angelgabrieljacintohuayllasco/G-Mini-Agent-Home/hardware/templates/pyramid-laptop-15.6-pieces.dxf

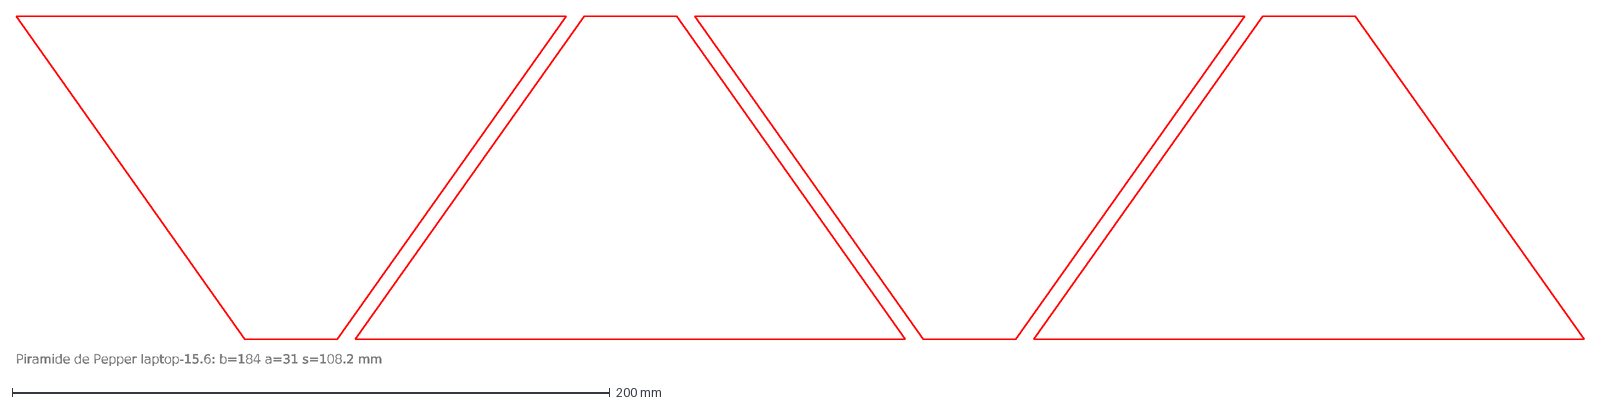
[picture p23: CAD file, 2026-10-08]
hardware/templates/pyramid-laptop-15.6-pieces.dxf
Piramide de Pepper laptop-15.6: b=184 a=31 s=108.2 mm
