angelgabrieljacintohuayllasco/G-Mini-Agent-Home/hardware/templates/pyramid-tv-32-net.dxf

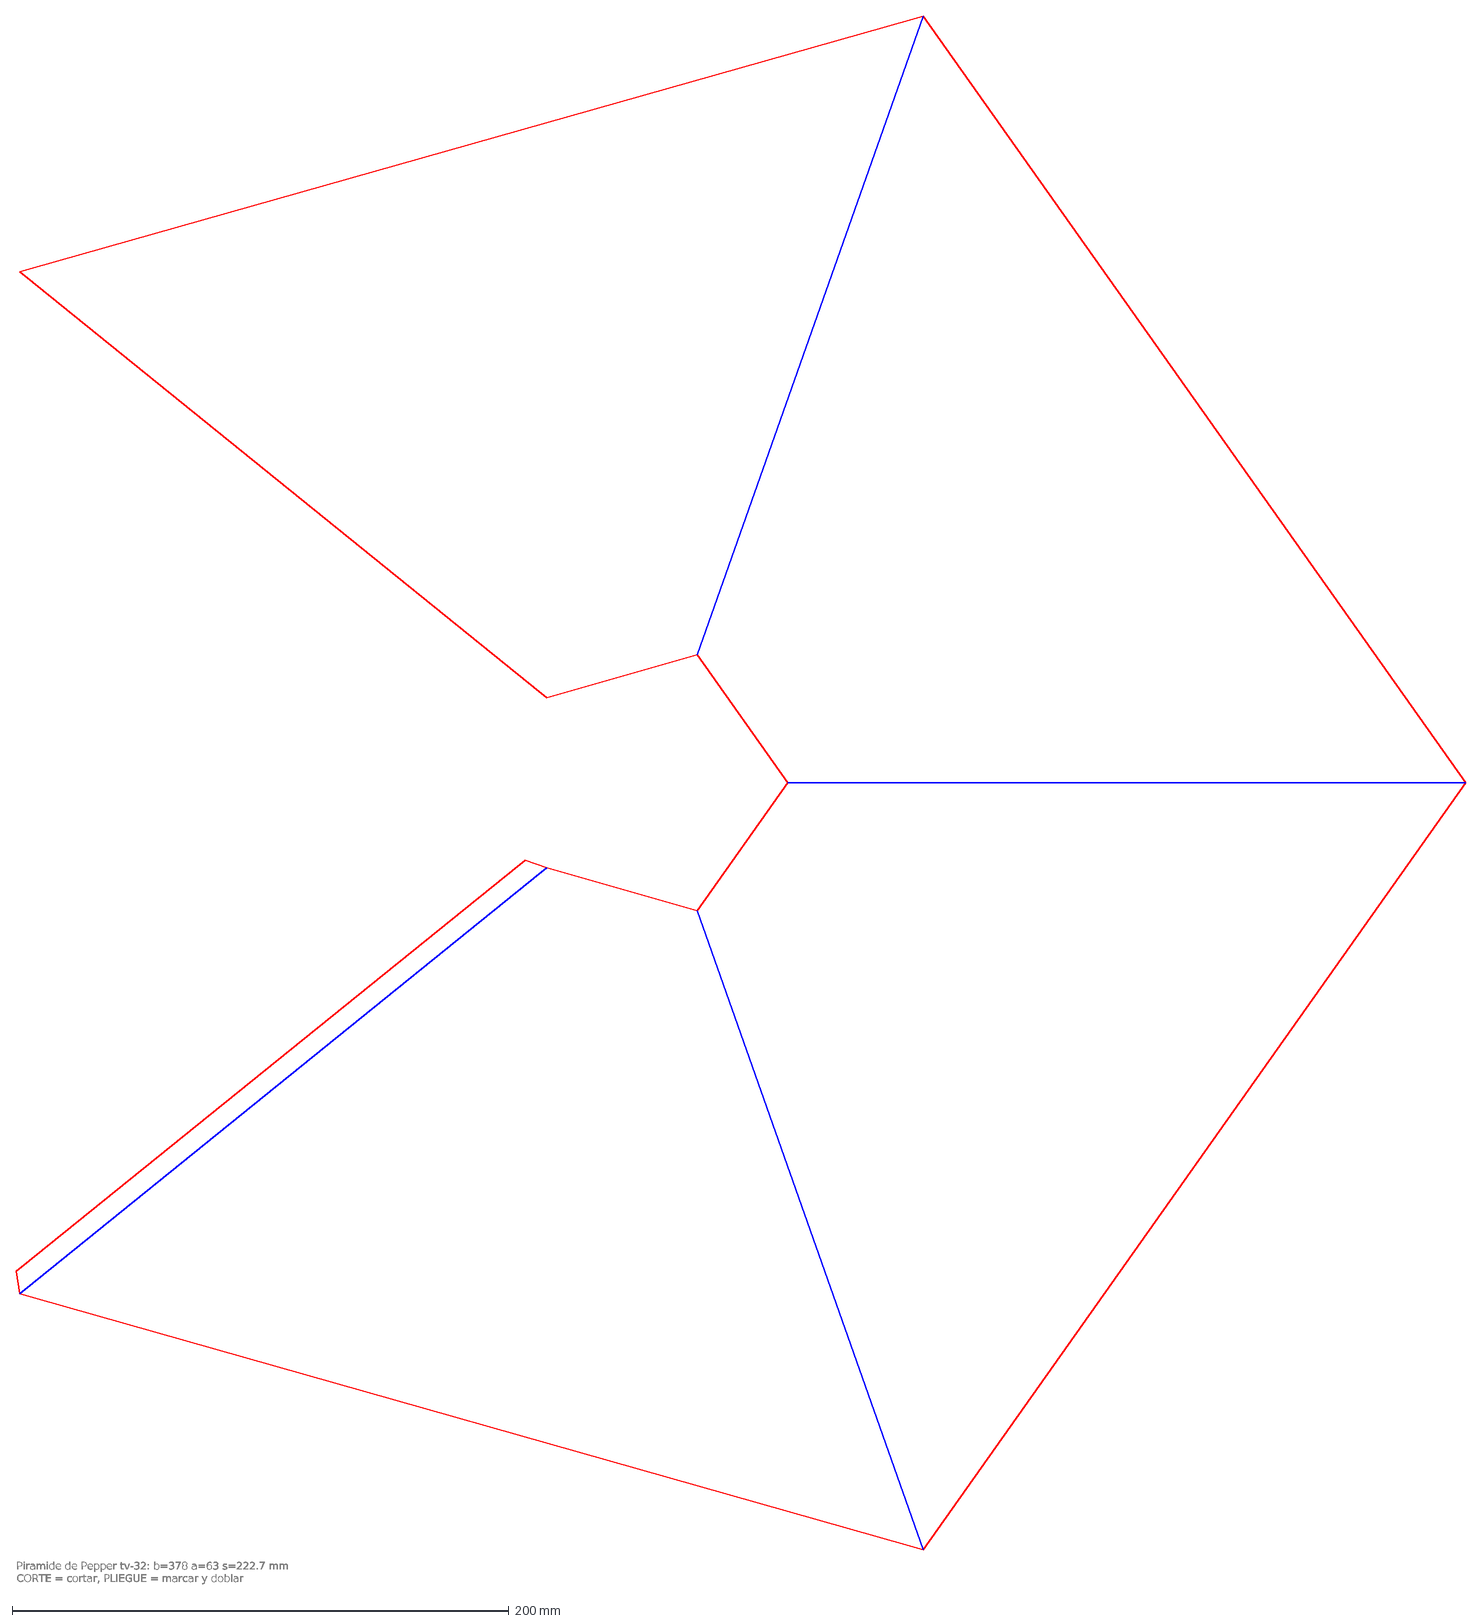
[picture p24: CAD file, 2026-10-08]
hardware/templates/pyramid-tv-32-net.dxf
Piramide de Pepper tv-32: b=378 a=63 s=222.7 mm
CORTE = cortar, PLIEGUE = marcar y doblar
