angelgabrieljacintohuayllasco/G-Mini-Agent-Home/hardware/templates/pyramid-tablet-11-pieces.dxf

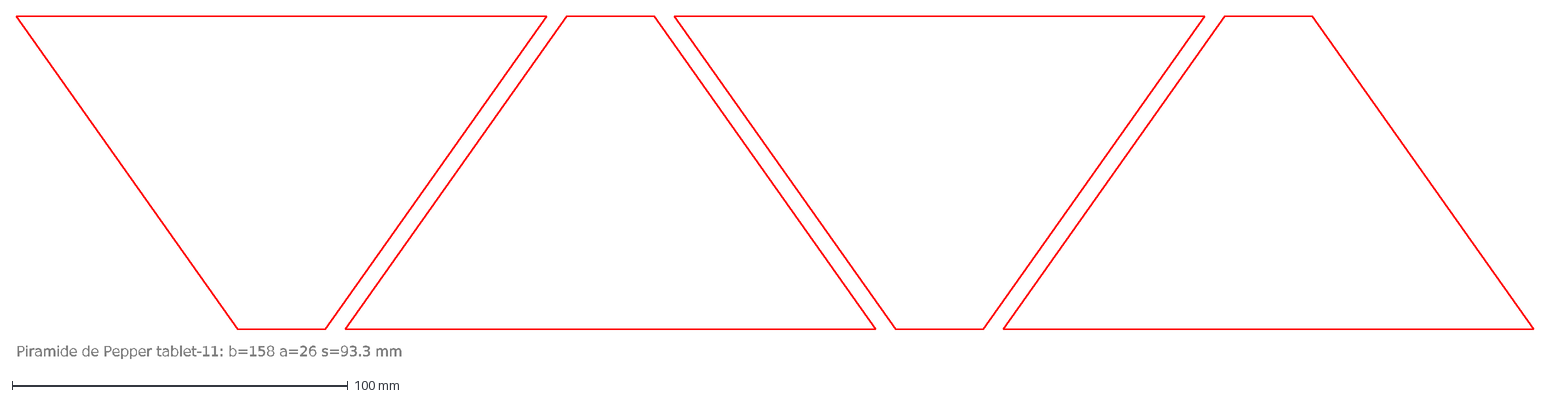
[picture p25: CAD file, 2026-10-08]
hardware/templates/pyramid-tablet-11-pieces.dxf
Piramide de Pepper tablet-11: b=158 a=26 s=93.3 mm
