angelgabrieljacintohuayllasco/G-Mini-Agent-Home/hardware/templates/pyramid-phone-6.1-net.dxf

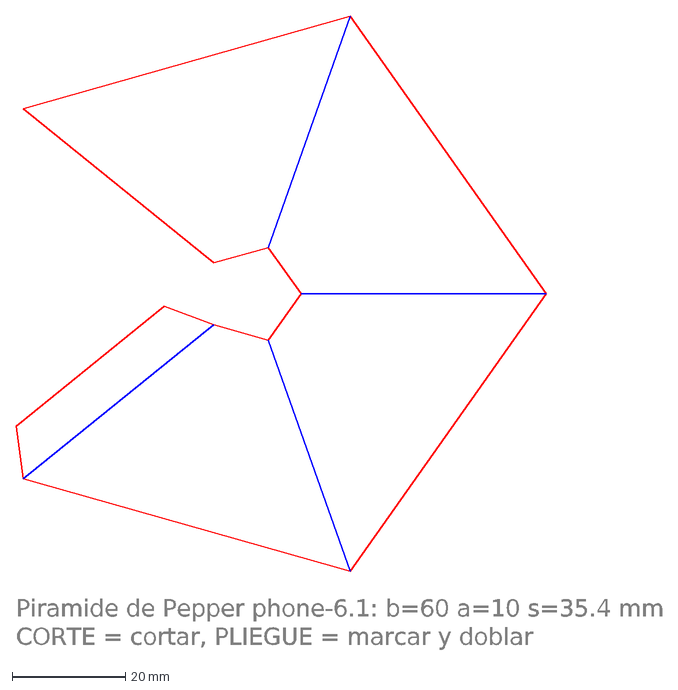
[picture p26: CAD file, 2026-10-08]
hardware/templates/pyramid-phone-6.1-net.dxf
Piramide de Pepper phone-6.1: b=60 a=10 s=35.4 mm
CORTE = cortar, PLIEGUE = marcar y doblar
