angelgabrieljacintohuayllasco/G-Mini-Agent-Home/hardware/templates/pyramid-tablet-11-net.dxf

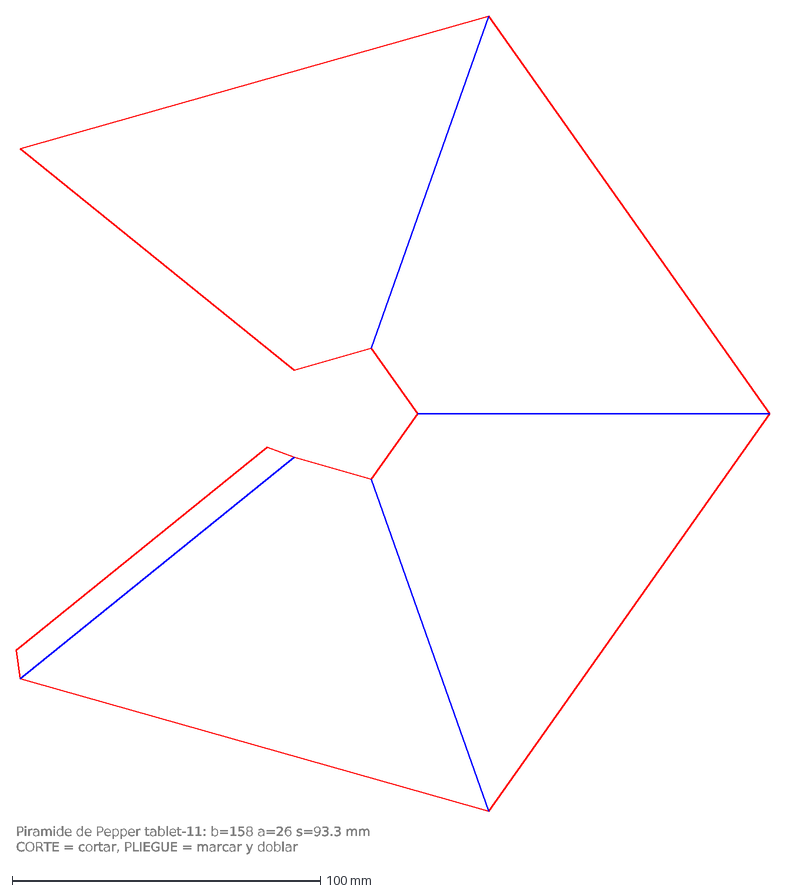
[picture p27: CAD file, 2026-10-08]
hardware/templates/pyramid-tablet-11-net.dxf
Piramide de Pepper tablet-11: b=158 a=26 s=93.3 mm
CORTE = cortar, PLIEGUE = marcar y doblar
