angelgabrieljacintohuayllasco/G-Mini-Agent-Home/hardware/templates/pyramid-phone-6.1-pieces.dxf

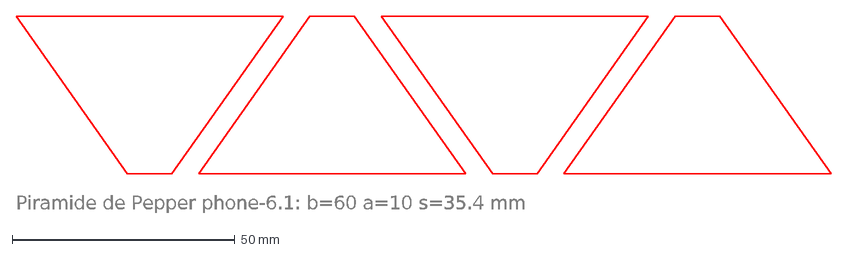
[picture p29: CAD file, 2026-10-08]
hardware/templates/pyramid-phone-6.1-pieces.dxf
Piramide de Pepper phone-6.1: b=60 a=10 s=35.4 mm
