angelgabrieljacintohuayllasco/G-Mini-Agent-Home/hardware/templates/pyramid-tablet-10-pieces.dxf

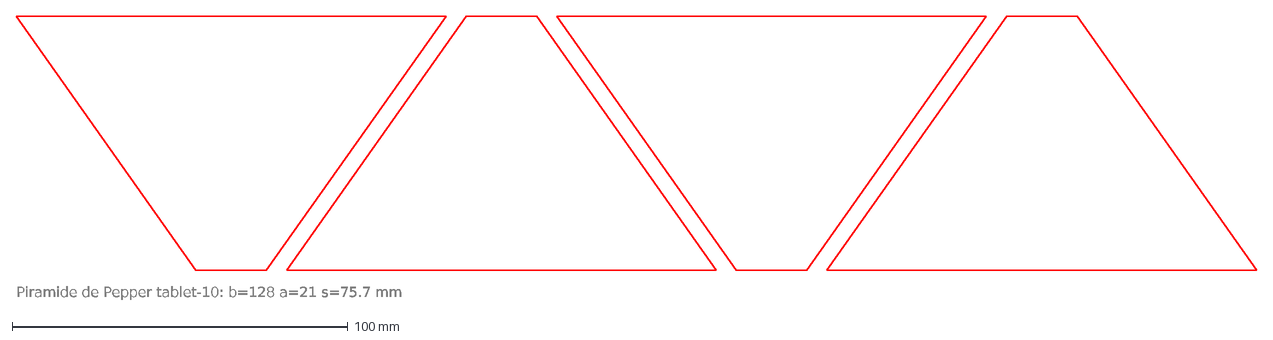
[picture p30: CAD file, 2026-10-08]
hardware/templates/pyramid-tablet-10-pieces.dxf
Piramide de Pepper tablet-10: b=128 a=21 s=75.7 mm
