angelgabrieljacintohuayllasco/G-Mini-Agent-Home/firmware/esp32-companion/include/gmini_wm_strings_es.h

/**
 * gmini_wm_strings_es.h
 * Textos en español del portal de WiFiManager para G-Mini Home.
 *
 * Traducción de wm_strings_en.h de WiFiManager 2.0.17
 * (https://github.com/tzapu/WiFiManager, licencia MIT, autores tzapu y
 * tablatronix). Se activa con el build flag
 *   -DWM_STRINGS_FILE="\"gmini_wm_strings_es.h\""
 * Si se actualiza WiFiManager, comparar con su wm_strings_en.h: este archivo
 * tiene que definir los mismos símbolos o el firmware no compila.
 * Los acentos van como entidades HTML porque los textos se sirven en HTML.
 */

#ifndef _GMINI_WM_STRINGS_ES_H_
#define _GMINI_WM_STRINGS_ES_H_


#ifndef WIFI_MANAGER_OVERRIDE_STRINGS
// !!! ABOVE WILL NOT WORK if you define in your sketch, must be build flag, if anyone one knows how to order includes to be able to do this it would be neat.. I have seen it done..

// strings files must include a consts file!
#include "wm_consts_en.h" // include constants, tokens, routes

const char WM_LANGUAGE[] PROGMEM = "es"; // i18n lang code

const char HTTP_HEAD_START[]       PROGMEM = "<!DOCTYPE html>"
"<html lang='es'><head>"
"<meta name='format-detection' content='telephone=no'>"
"<meta charset='UTF-8'>"
"<meta  name='viewport' content='width=device-width,initial-scale=1,user-scalable=no'/>"
"<title>{v}</title>";

const char HTTP_SCRIPT[]           PROGMEM = "<script>function c(l){"
"document.getElementById('s').value=l.getAttribute('data-ssid')||l.innerText||l.textContent;"
"p = l.nextElementSibling.classList.contains('l');"
"document.getElementById('p').disabled = !p;"
"if(p)document.getElementById('p').focus();};"
"function f() {var x = document.getElementById('p');x.type==='password'?x.type='text':x.type='password';}"
"</script>"; // @todo add button states, disable on click , show ack , spinner etc

const char HTTP_HEAD_END[]         PROGMEM = "</head><body class='{c}'><div class='wrap'>"; // {c} = _bodyclass
// example of embedded logo, base64 encoded inline, No styling here
// const char HTTP_ROOT_MAIN[]        PROGMEM = "<img title=' alt=' src='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' /><h1>{v}</h1><h3>WiFiManager</h3>";
const char HTTP_ROOT_MAIN[]        PROGMEM = "<h1>{t}</h1><h3>{v}</h3>";

const char * const HTTP_PORTAL_MENU[] PROGMEM = {
"<form action='/wifi'    method='get'><button>Configurar WiFi</button></form><br/>\n", // MENU_WIFI
"<form action='/0wifi'   method='get'><button>Configurar WiFi (sin buscar redes)</button></form><br/>\n", // MENU_WIFINOSCAN
"<form action='/info'    method='get'><button>Informaci&oacute;n</button></form><br/>\n", // MENU_INFO
"<form action='/param'   method='get'><button>Ajustes</button></form><br/>\n",//MENU_PARAM
"<form action='/close'   method='get'><button>Cerrar</button></form><br/>\n", // MENU_CLOSE
"<form action='/restart' method='get'><button>Reiniciar</button></form><br/>\n",// MENU_RESTART
"<form action='/exit'    method='get'><button>Salir</button></form><br/>\n",  // MENU_EXIT
"<form action='/erase'   method='get'><button class='D'>Borrar</button></form><br/>\n", // MENU_ERASE
"<form action='/update'  method='get'><button>Actualizar firmware</button></form><br/>\n",// MENU_UPDATE
"<hr><br/>" // MENU_SEP
};

// const char HTTP_PORTAL_OPTIONS[]   PROGMEM = strcat(HTTP_PORTAL_MENU[0] , HTTP_PORTAL_MENU[3] , HTTP_PORTAL_MENU[7]);
const char HTTP_PORTAL_OPTIONS[]   PROGMEM = "";
const char HTTP_ITEM_QI[]          PROGMEM = "<div role='img' aria-label='{r}%' title='{r}%' class='q q-{q} {i} {h}'></div>"; // rssi icons
const char HTTP_ITEM_QP[]          PROGMEM = "<div class='q {h}'>{r}%</div>"; // rssi percentage {h} = hidden showperc pref
const char HTTP_ITEM[]             PROGMEM = "<div><a href='#p' onclick='c(this)' data-ssid='{V}'>{v}</a>{qi}{qp}</div>"; // {q} = HTTP_ITEM_QI, {r} = HTTP_ITEM_QP
// const char HTTP_ITEM[]            PROGMEM = "<div><a href='#p' onclick='c(this)'>{v}</a> {R} {r}% {q} {e}</div>"; // test all tokens

const char HTTP_FORM_START[]       PROGMEM = "<form method='POST' action='{v}'>";
const char HTTP_FORM_WIFI[]        PROGMEM = "<label for='s'>Red WiFi (SSID)</label><input id='s' name='s' maxlength='32' autocorrect='off' autocapitalize='none' placeholder='{v}'><br/><label for='p'>Contrase&ntilde;a</label><input id='p' name='p' maxlength='64' type='password' placeholder='{p}'><input type='checkbox' id='showpass' onclick='f()'> <label for='showpass'>Mostrar contrase&ntilde;a</label><br/>";
const char HTTP_FORM_WIFI_END[]    PROGMEM = "";
const char HTTP_FORM_STATIC_HEAD[] PROGMEM = "<hr><br/>";
const char HTTP_FORM_END[]         PROGMEM = "<br/><br/><button type='submit'>Guardar</button></form>";
const char HTTP_FORM_LABEL[]       PROGMEM = "<label for='{i}'>{t}</label>";
const char HTTP_FORM_PARAM_HEAD[]  PROGMEM = "<hr><br/>";
const char HTTP_FORM_PARAM[]       PROGMEM = "<br/><input id='{i}' name='{n}' maxlength='{l}' value='{v}' {c}>\n"; // do not remove newline!

const char HTTP_SCAN_LINK[]        PROGMEM = "<br/><form action='/wifi?refresh=1' method='POST'><button name='refresh' value='1'>Buscar redes de nuevo</button></form>";
const char HTTP_SAVED[]            PROGMEM = "<div class='msg'>Guardando los datos<br/>El dispositivo intenta conectarse a tu red.<br />Si no lo logra, vuelve a conectarte a su red WiFi y prueba otra vez.</div>";
const char HTTP_PARAMSAVED[]       PROGMEM = "<div class='msg S'>Guardado<br/></div>";
const char HTTP_END[]              PROGMEM = "</div></body></html>";
const char HTTP_ERASEBTN[]         PROGMEM = "<br/><form action='/erase' method='get'><button class='D'>Borrar la configuraci&oacute;n WiFi</button></form>";
const char HTTP_UPDATEBTN[]        PROGMEM = "<br/><form action='/update' method='get'><button>Actualizar firmware</button></form>";
const char HTTP_BACKBTN[]          PROGMEM = "<hr><br/><form action='/' method='get'><button>Volver</button></form>";

const char HTTP_STATUS_ON[]        PROGMEM = "<div class='msg S'><strong>Conectado</strong> a {v}<br/><em><small>con la IP {i}</small></em></div>";
const char HTTP_STATUS_OFF[]       PROGMEM = "<div class='msg {c}'><strong>Sin conexi&oacute;n</strong> a {v}{r}</div>"; // {c=class} {v=ssid} {r=status_off}
const char HTTP_STATUS_OFFPW[]     PROGMEM = "<br/>Contrase&ntilde;a incorrecta"; // STATION_WRONG_PASSWORD,  no eps32
const char HTTP_STATUS_OFFNOAP[]   PROGMEM = "<br/>No se encontr&oacute; la red";   // WL_NO_SSID_AVAIL
const char HTTP_STATUS_OFFFAIL[]   PROGMEM = "<br/>No se pudo conectar"; // WL_CONNECT_FAILED
const char HTTP_STATUS_NONE[]      PROGMEM = "<div class='msg'>Todav&iacute;a no hay una red configurada</div>";
const char HTTP_BR[]               PROGMEM = "<br/>";

const char HTTP_STYLE[]            PROGMEM = "<style>"
".c,body{text-align:center;font-family:verdana}div,input,select{padding:5px;font-size:1em;margin:5px 0;box-sizing:border-box}"
"input,button,select,.msg{border-radius:.3rem;width: 100%}input[type=radio],input[type=checkbox]{width:auto}"
"button,input[type='button'],input[type='submit']{cursor:pointer;border:0;background-color:#1fa3ec;color:#fff;line-height:2.4rem;font-size:1.2rem;width:100%}"
"input[type='file']{border:1px solid #1fa3ec}"
".wrap {text-align:left;display:inline-block;min-width:260px;max-width:500px}"
// links
"a{color:#000;font-weight:700;text-decoration:none}a:hover{color:#1fa3ec;text-decoration:underline}"
// quality icons
".q{height:16px;margin:0;padding:0 5px;text-align:right;min-width:38px;float:right}.q.q-0:after{background-position-x:0}.q.q-1:after{background-position-x:-16px}.q.q-2:after{background-position-x:-32px}.q.q-3:after{background-position-x:-48px}.q.q-4:after{background-position-x:-64px}.q.l:before{background-position-x:-80px;padding-right:5px}.ql .q{float:left}.q:after,.q:before{content:'';width:16px;height:16px;display:inline-block;background-repeat:no-repeat;background-position: 16px 0;"
"background-image:url('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');}"
// icons @2x media query (32px rescaled)
"@media (-webkit-min-device-pixel-ratio: 2),(min-resolution: 192dpi){.q:before,.q:after {"
"background-image:url('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');"
"background-size: 95px 16px;}}"
// msg callouts
".msg{padding:20px;margin:20px 0;border:1px solid #eee;border-left-width:5px;border-left-color:#777}.msg h4{margin-top:0;margin-bottom:5px}.msg.P{border-left-color:#1fa3ec}.msg.P h4{color:#1fa3ec}.msg.D{border-left-color:#dc3630}.msg.D h4{color:#dc3630}.msg.S{border-left-color: #5cb85c}.msg.S h4{color: #5cb85c}"
// lists
"dt{font-weight:bold}dd{margin:0;padding:0 0 0.5em 0;min-height:12px}"
"td{vertical-align: top;}"
".h{display:none}"
"button{transition: 0s opacity;transition-delay: 3s;transition-duration: 0s;cursor: pointer}"
"button.D{background-color:#dc3630}"
"button:active{opacity:50% !important;cursor:wait;transition-delay: 0s}"
// invert
"body.invert,body.invert a,body.invert h1 {background-color:#060606;color:#fff;}"
"body.invert .msg{color:#fff;background-color:#282828;border-top:1px solid #555;border-right:1px solid #555;border-bottom:1px solid #555;}"
"body.invert .q[role=img]{-webkit-filter:invert(1);filter:invert(1);}"
":disabled {opacity: 0.5;}"
"</style>";

#ifndef WM_NOHELP
const char HTTP_HELP[]             PROGMEM =
 "<br/><h3>P&aacute;ginas disponibles</h3><hr>"
 "<table class='table'>"
 "<thead><tr><th>P&aacute;gina</th><th>Funci&oacute;n</th></tr></thead><tbody>"
 "<tr><td><a href='/'>/</a></td>"
 "<td>Men&uacute; principal.</td></tr>"
 "<tr><td><a href='/wifi'>/wifi</a></td>"
 "<td>Muestra las redes encontradas y permite configurar el WiFi (/0wifi, sin buscar redes).</td></tr>"
 "<tr><td><a href='/wifisave'>/wifisave</a></td>"
 "<td>Guarda la configuraci&oacute;n WiFi y configura el dispositivo. Necesita los datos del formulario.</td></tr>"
 "<tr><td><a href='/param'>/param</a></td>"
 "<td>Ajustes</td></tr>"
 "<tr><td><a href='/info'>/info</a></td>"
 "<td>Informaci&oacute;n</td></tr>"
 "<tr><td><a href='/u'>/u</a></td>"
 "<td>Actualizaci&oacute;n por OTA</td></tr>"
 "<tr><td><a href='/close'>/close</a></td>"
 "<td>Cierra la ventana del portal cautivo; el portal sigue activo.</td></tr>"
 "<tr><td>/exit</td>"
 "<td>Sale del portal de configuraci&oacute;n y lo cierra.</td></tr>"
 "<tr><td>/restart</td>"
 "<td>Reinicia el dispositivo.</td></tr>"
 "<tr><td>/erase</td>"
 "<td>Borra la configuraci&oacute;n WiFi y reinicia. El dispositivo no se conectar&aacute; a ninguna red hasta que configures una nueva.</td></tr>"
 "</table>"
 "<p/>Github <a href='https://github.com/tzapu/WiFiManager'>https://github.com/tzapu/WiFiManager</a>.";
#else
const char HTTP_HELP[]             PROGMEM = "";
#endif

const char HTTP_UPDATE[] PROGMEM = "Subir un firmware nuevo<br/><form method='POST' action='u' enctype='multipart/form-data' onchange=\"(function(el){document.getElementById('uploadbin').style.display = el.value=='' ? 'none' : 'initial';})(this)\"><input type='file' name='update' accept='.bin,application/octet-stream'><button id='uploadbin' type='submit' class='h D'>Actualizar</button></form><small><a href='http://192.168.4.1/update' target='_blank'>* Puede no funcionar dentro del portal cautivo: &aacute;brelo en el navegador, http://192.168.4.1</a><small>";
const char HTTP_UPDATE_FAIL[] PROGMEM = "<div class='msg D'><strong>&iexcl;Fall&oacute; la actualizaci&oacute;n!</strong><Br/>Reinicia el dispositivo e int&eacute;ntalo de nuevo</div>";
const char HTTP_UPDATE_SUCCESS[] PROGMEM = "<div class='msg S'><strong>Actualizaci&oacute;n completa.</strong> <br/> El dispositivo se est&aacute; reiniciando...</div>";

#ifdef WM_JSTEST
const char HTTP_JS[] PROGMEM =
"<script>function postAjax(url, data, success) {"
"    var params = typeof data == 'string' ? data : Object.keys(data).map("
"            function(k){ return encodeURIComponent(k) + '=' + encodeURIComponent(data[k]) }"
"        ).join('&');"
"    var xhr = window.XMLHttpRequest ? new XMLHttpRequest() : new ActiveXObject(\"Microsoft.XMLHTTP\");"
"    xhr.open('POST', url);"
"    xhr.onreadystatechange = function() {"
"        if (xhr.readyState>3 && xhr.status==200) { success(xhr.responseText); }"
"    };"
"    xhr.setRequestHeader('X-Requested-With', 'XMLHttpRequest');"
"    xhr.setRequestHeader('Content-Type', 'application/x-www-form-urlencoded');"
"    xhr.send(params);"
"    return xhr;}"
"postAjax('/status', 'p1=1&p2=Hello+World', function(data){ console.log(data); });"
"postAjax('/status', { p1: 1, p2: 'Hello World' }, function(data){ console.log(data); });"
"</script>";
#endif

// Info html
// @todo remove html elements from progmem, repetetive strings
#ifdef ESP32
	const char HTTP_INFO_esphead[]    PROGMEM = "<h3>esp32</h3><hr><dl>";
	const char HTTP_INFO_chiprev[]    PROGMEM = "<dt>Revisi&oacute;n del chip</dt><dd>{1}</dd>";
  	const char HTTP_INFO_lastreset[]  PROGMEM = "<dt>Motivo del &uacute;ltimo reinicio</dt><dd>CPU0: {1}<br/>CPU1: {2}</dd>";
  	const char HTTP_INFO_aphost[]     PROGMEM = "<dt>Nombre del punto de acceso</dt><dd>{1}</dd>";
    const char HTTP_INFO_psrsize[]    PROGMEM = "<dt>Tama&ntilde;o de la PSRAM</dt><dd>{1} bytes</dd>";
	const char HTTP_INFO_temp[]       PROGMEM = "<dt>Temperatura</dt><dd>{1} C&deg; / {2} F&deg;</dd>";
    const char HTTP_INFO_hall[]       PROGMEM = "<dt>Sensor Hall</dt><dd>{1}</dd>";
#else
	const char HTTP_INFO_esphead[]    PROGMEM = "<h3>esp8266</h3><hr><dl>";
	const char HTTP_INFO_fchipid[]    PROGMEM = "<dt>ID del chip de flash</dt><dd>{1}</dd>";
	const char HTTP_INFO_corever[]    PROGMEM = "<dt>Versi&oacute;n del core</dt><dd>{1}</dd>";
	const char HTTP_INFO_bootver[]    PROGMEM = "<dt>Versi&oacute;n del arranque</dt><dd>{1}</dd>";
	const char HTTP_INFO_lastreset[]  PROGMEM = "<dt>Motivo del &uacute;ltimo reinicio</dt><dd>{1}</dd>";
	const char HTTP_INFO_flashsize[]  PROGMEM = "<dt>Tama&ntilde;o real de la flash</dt><dd>{1} bytes</dd>";
#endif

const char HTTP_INFO_memsmeter[]  PROGMEM = "<br/><progress value='{1}' max='{2}'></progress></dd>";
const char HTTP_INFO_memsketch[]  PROGMEM = "<dt>Memoria: tama&ntilde;o del programa</dt><dd>Usados / total (bytes)<br/>{1} / {2}";
const char HTTP_INFO_freeheap[]   PROGMEM = "<dt>Memoria libre (heap)</dt><dd>{1} bytes disponibles</dd>";
const char HTTP_INFO_wifihead[]   PROGMEM = "<br/><h3>WiFi</h3><hr>";
const char HTTP_INFO_uptime[]     PROGMEM = "<dt>Tiempo encendido</dt><dd>{1} min {2} s</dd>";
const char HTTP_INFO_chipid[]     PROGMEM = "<dt>ID del chip</dt><dd>{1}</dd>";
const char HTTP_INFO_idesize[]    PROGMEM = "<dt>Tama&ntilde;o de la flash</dt><dd>{1} bytes</dd>";
const char HTTP_INFO_sdkver[]     PROGMEM = "<dt>Versi&oacute;n del SDK</dt><dd>{1}</dd>";
const char HTTP_INFO_cpufreq[]    PROGMEM = "<dt>Frecuencia de la CPU</dt><dd>{1}MHz</dd>";
const char HTTP_INFO_apip[]       PROGMEM = "<dt>IP del punto de acceso</dt><dd>{1}</dd>";
const char HTTP_INFO_apmac[]      PROGMEM = "<dt>MAC del punto de acceso</dt><dd>{1}</dd>";
const char HTTP_INFO_apssid[]     PROGMEM = "<dt>Red del punto de acceso (SSID)</dt><dd>{1}</dd>";
const char HTTP_INFO_apbssid[]    PROGMEM = "<dt>BSSID</dt><dd>{1}</dd>";
const char HTTP_INFO_stassid[]    PROGMEM = "<dt>Red conectada (SSID)</dt><dd>{1}</dd>";
const char HTTP_INFO_staip[]      PROGMEM = "<dt>IP en la red</dt><dd>{1}</dd>";
const char HTTP_INFO_stagw[]      PROGMEM = "<dt>Puerta de enlace</dt><dd>{1}</dd>";
const char HTTP_INFO_stasub[]     PROGMEM = "<dt>M&aacute;scara de subred</dt><dd>{1}</dd>";
const char HTTP_INFO_dnss[]       PROGMEM = "<dt>Servidor DNS</dt><dd>{1}</dd>";
const char HTTP_INFO_host[]       PROGMEM = "<dt>Nombre del equipo</dt><dd>{1}</dd>";
const char HTTP_INFO_stamac[]     PROGMEM = "<dt>MAC en la red</dt><dd>{1}</dd>";
const char HTTP_INFO_conx[]       PROGMEM = "<dt>Conectado</dt><dd>{1}</dd>";
const char HTTP_INFO_autoconx[]   PROGMEM = "<dt>Conexi&oacute;n autom&aacute;tica</dt><dd>{1}</dd>";

const char HTTP_INFO_aboutver[]     PROGMEM = "<dt>WiFiManager</dt><dd>{1}</dd>";
const char HTTP_INFO_aboutarduino[] PROGMEM = "<dt>Arduino</dt><dd>{1}</dd>";
const char HTTP_INFO_aboutsdk[]     PROGMEM = "<dt>ESP-SDK/IDF</dt><dd>{1}</dd>";
const char HTTP_INFO_aboutdate[]    PROGMEM = "<dt>Fecha de compilaci&oacute;n</dt><dd>{1}</dd>";

const char S_brand[]              PROGMEM = "WiFiManager";
const char S_debugPrefix[]        PROGMEM = "*wm:";
const char S_y[]                  PROGMEM = "S&iacute;";
const char S_n[]                  PROGMEM = "No";
const char S_enable[]             PROGMEM = "Activado";
const char S_disable[]            PROGMEM = "Desactivado";
const char S_GET[]                PROGMEM = "GET";
const char S_POST[]               PROGMEM = "POST";
const char S_NA[]                 PROGMEM = "Desconocido";
const char S_passph[]             PROGMEM = "********";
const char S_titlewifisaved[]     PROGMEM = "Datos guardados";
const char S_titlewifisettings[]  PROGMEM = "Ajustes guardados";
const char S_titlewifi[]          PROGMEM = "Configurar WiFi";
const char S_titleinfo[]          PROGMEM = "Informaci&oacute;n";
const char S_titleparam[]         PROGMEM = "Ajustes";
const char S_titleparamsaved[]    PROGMEM = "Ajustes guardados";
const char S_titleexit[]          PROGMEM = "Salir";
const char S_titlereset[]         PROGMEM = "Reiniciar";
const char S_titleerase[]         PROGMEM = "Borrar";
const char S_titleclose[]         PROGMEM = "Cerrar";
const char S_options[]            PROGMEM = "opciones";
const char S_nonetworks[]         PROGMEM = "No se encontraron redes. Pulsa Buscar redes de nuevo.";
const char S_staticip[]           PROGMEM = "IP fija";
const char S_staticgw[]           PROGMEM = "Puerta de enlace fija";
const char S_staticdns[]          PROGMEM = "DNS fijo";
const char S_subnet[]             PROGMEM = "Subred";
const char S_exiting[]            PROGMEM = "Saliendo";
const char S_resetting[]          PROGMEM = "El dispositivo se reiniciar&aacute; en unos segundos.";
const char S_closing[]            PROGMEM = "Puedes cerrar esta p&aacute;gina; el portal sigue activo.";
const char S_error[]              PROGMEM = "Ocurri&oacute; un error";
const char S_notfound[]           PROGMEM = "Archivo no encontrado\n\n";
const char S_uri[]                PROGMEM = "URI: ";
const char S_method[]             PROGMEM = "\nMetodo: ";
const char S_args[]               PROGMEM = "\nArgumentos: ";
const char S_parampre[]           PROGMEM = "param_";

// debug strings
const char D_HR[]                 PROGMEM = "--------------------";


// softap ssid default prefix
#ifdef ESP8266
    const char S_ssidpre[]        PROGMEM = "ESP";
#elif defined(ESP32)
    const char S_ssidpre[]        PROGMEM = "ESP32";
#else
    const char S_ssidpre[]        PROGMEM = "WM";
#endif

// END WIFI_MANAGER_OVERRIDE_STRINGS
#endif

#endif
